TTtensan/NERD-HPC/software/src/basic.cpp

/*
 TOYOSHIKI Tiny BASIC for Arduino
 (C)2012 Tetsuya Suzuki
 GNU General Public License
 */

#include <stdlib.h>
#include <stdio.h>
#include "tusb.h"
#include "lcd.h"
#include "f_util.h"
#include "ff.h"
#include "font.h"
#include "diskio.h"
#include "sd.hpp"
#include "io.h"
#include "ir.h"
#include "ioexp.h"
#include "speaker.h"
#include "usb.h"
#include "basic.hpp"
#include "pin.h"

#define _FONT_
#define _SLEEP_
#define _PROG_
#define _LCD_
#define _USB_
#define _IO_
#define _IR_
#define _IOEXP_
#define _SPEAKER_

// TOYOSHIKI TinyBASIC symbols
// TO-DO Rewrite defined values to fit your machine as needed
#define SIZE_LINE 128 //Command line buffer length + NULL
#define SIZE_IBUF 128 //i-code conversion buffer size
#define SIZE_LIST 32768 //List buffer size
#define SIZE_ARRY 256 //Array area size
#define SIZE_GSTK 20 //GOSUB stack size(2/nest)
#define SIZE_LSTK 50 //FOR stack size(5/nest)

// Depending on device functions
// TO-DO Rewrite these functions to fit your machine
#define STR_EDITION "NERD HPC"
#define STR_VERSION "1.13.7"

// Terminal control
#define c_putch(c) putch2(c)
#define c_getch( ) getch2()
#define c_kbhit( ) kbhit2()

// シリアル出力のバッファ。
// 1文字ごとにprintf()を呼ぶと毎回stdioのロック取得とUSB CDCへの
// ブロッキング書き込みが走り、PRINTの実行時間の大半をここで使ってしまう。
// 改行かバッファが埋まるまで溜めて、まとめて書き出す
#define SIZE_OBUF 64
static char obuf[SIZE_OBUF];
static unsigned char obufi = 0;

void oflush() {
    if(obufi == 0) return;
    fwrite(obuf, 1, obufi, stdout);
    obufi = 0;
    fflush(stdout);
}

void putch2(char c) {
    obuf[obufi++] = c;
    if(obufi >= SIZE_OBUF || c == '\n') oflush();
    lcd_print_c_auto(c, black);
}

char getch2() {
    oflush(); // 入力待ちに入る前に溜まっている分を吐き出す
    while(true) {
        if(ioexp_getchr_available()) return ioexp_getchr();
        else if(tud_cdc_available()) return getchar();
    }
}

uint32_t kbhit2() {
    if(ioexp_getchr_available() || tud_cdc_available()) return 1;
    else return 0;
}

#define KEY_ENTER 13
void newline(void) {
  c_putch(13); //CR
  c_putch(10); //LF
}

// Return random number
short getrnd(short value) {
  return rand()%value + 1;
}

// Prototypes (necessity minimum)
short iexp(void);
void iload();

// Keyword table
const char *kwtbl[] = {
  "GOTO", "GOSUB", "RETURN",
  "FOR", "TO", "STEP", "NEXT",
  "IF", "REM", "STOP",
  "INPUT", "PRINT", "LET",
  ",", ";",
  "-", "+", "*", "/", "%", "(", ")",
  "$", "`", "<<", ">>",
  "&", "|", "^", "~",
  ">=", "#", ">", "=", "<=", "<",
  "@", "RND", "ABS", "SIZE",
#ifdef _FONT_
  "SETF",
  "RESETF",
#endif
#ifdef _SLEEP_
  "SLEEPMS",
  "SLEEPUS",
#endif
#ifdef _PROG_
  "SAVE", "LOAD", "DELETE",
#endif
#ifdef _LCD_
  "CLS",
  "GCLS",
  "VSYNC",
  "GPSET",
  "GLINE",
  "GRECT",
  "GCIRCLE",
  "GPLAYNM",
  "GPUTC",
  "CHR",
  "LOCATE",
  "SCR",
  "GPGET",
  "GTRI",
#endif
#ifdef _USB_
  "SNDKCD",
#endif
#ifdef _IO_
  "IOSD",
  "IOPUT",
  "IOGET",
  "IOPU",
  "IOPD",
  "IODP",
  "IOUS",
  "IOUR",
  "IOIIM",
  "IOIIS",
  "IOIS",
  "IOIR",
#endif
#ifdef _IR_
  "IRPUT",
  "IRGET",
#endif
#ifdef _IOEXP_
  "GKOPT",
  "GETKEY",
#endif
#ifdef _SPEAKER_
  "PLYSND",
  "STPSND",
#endif
  "LIST", "ALL", "RUN", "NEW"
};

// Keyword count
#define SIZE_KWTBL (sizeof(kwtbl) / sizeof(const char*))

// i-code(Intermediate code) assignment
enum {
  I_GOTO, I_GOSUB, I_RETURN,
  I_FOR, I_TO, I_STEP, I_NEXT,
  I_IF, I_REM, I_STOP,
  I_INPUT, I_PRINT, I_LET,
  I_COMMA, I_SEMI,
  I_MINUS, I_PLUS, I_MUL, I_DIV, I_MOD, I_OPEN, I_CLOSE,
  I_HEX, I_BIN, I_LSHIFT, I_RSHIFT,
  I_AND, I_OR, I_XOR, I_BITFLIP,
  I_GTE, I_SHARP, I_GT, I_EQ, I_LTE, I_LT,
  I_ARRAY, I_RND, I_ABS, I_SIZE,
#ifdef _FONT_
  I_SETF,
  I_RESETF,
#endif
#ifdef _SLEEP_
  I_SLEEPMS,
  I_SLEEPUS,
#endif
#ifdef _PROG_
  I_SAVE, I_LOAD, I_DELETE,
#endif
#ifdef _LCD_
  I_CLS,
  I_GCLS,
  I_VSYNC,
  I_GPSET,
  I_GLINE,
  I_GRECT,
  I_GCIRCLE,
  I_GPLAYNM,
  I_GPUTC,
  I_CHR,
  I_LOCATE,
  I_SCR,
  I_GPGET,
  I_GTRI,
#endif
#ifdef _USB_
  I_SNDKCD,
#endif
#ifdef _IO_
  I_IOSD,
  I_IOPUT,
  I_IOGET,
  I_IOPU,
  I_IOPD,
  I_IODP,
  I_IOUS,
  I_IOUR,
  I_IOIIM,
  I_IOIIS,
  I_IOIS,
  I_IOIR,
#endif
#ifdef _IR_
  I_IRPUT,
  I_IRGET,
#endif
#ifdef _IOEXP_
  I_GKOPT,
  I_GETKEY,
#endif
#ifdef _SPEAKER_
  I_PLYSND,
  I_STPSND,
#endif
  I_LIST, I_ALL, I_RUN, I_NEW,
  I_NUM, I_HEXNUM, I_BINNUM, I_VAR, I_STR,
  I_EOL
};

// List formatting condition
// 後ろに空白を入れない中間コード
const unsigned char i_nsa[] = {
  I_RETURN, I_STOP, I_COMMA,
  I_MINUS, I_PLUS, I_MUL, I_DIV, I_MOD, I_OPEN, I_CLOSE,
  I_HEX, I_BIN, I_LSHIFT, I_RSHIFT,
  I_AND, I_OR, I_XOR, I_BITFLIP,
  I_GTE, I_SHARP, I_GT, I_EQ, I_LTE, I_LT,
#ifdef _FONT_
  I_RESETF,
#endif
#ifdef _LCD_
  I_CLS,
  I_GCLS,
  I_VSYNC,
  I_SCR,
  I_GPGET,
#endif
#ifdef _IO_
  I_IOGET,
  I_IOUR,
  I_IOIIM,
  I_IOIIS,
  I_IOIR,
#endif
#ifdef _IR_
  I_IRGET,
#endif
#ifdef _IOEXP_
  I_GETKEY,
#endif
#ifdef _SPEAKER_
  I_STPSND,
#endif
  I_ARRAY, I_RND, I_ABS, I_SIZE, I_ALL
};

// 前が定数か変数のとき前の空白をなくす中間コード
const unsigned char i_nsb[] = {
  I_MINUS, I_PLUS, I_MUL, I_DIV, I_MOD, I_OPEN, I_CLOSE,
  I_HEX, I_BIN, I_LSHIFT, I_RSHIFT,
  I_AND, I_OR, I_XOR, I_BITFLIP,
  I_GTE, I_SHARP, I_GT, I_EQ, I_LTE, I_LT,
  I_COMMA, I_SEMI, I_EOL
};

// exception search function
char sstyle(unsigned char code,
  const unsigned char *table, unsigned char count) {
  while(count--) //中間コードの数だけ繰り返す
    if (code == table[count]) //もし該当の中間コードがあったら
      return 1; //1を持ち帰る
  return 0; //（なければ）0を持ち帰る
}

// exception search macro
#define nospacea(c) sstyle(c, i_nsa, sizeof(i_nsa))
#define nospaceb(c) sstyle(c, i_nsb, sizeof(i_nsb))

// Error messages
unsigned char err;// Error message index
const char* errmsg[] = {
  "OK",
  "Devision by zero",
  "Overflow",
  "Subscript out of range",
  "Icode buffer full",
  "List full",
  "GOSUB too many nested",
  "RETURN stack underflow",
  "FOR too many nested",
  "NEXT without FOR",
  "NEXT without counter",
  "NEXT mismatch FOR",
  "FOR without variable",
  "FOR without TO",
  "LET without variable",
  "IF without condition",
  "Undefined line number",
  "\'(\' or \')\' expected",
  "\'=\' expected",
  "Illegal command",
  "Syntax error",
  "Internal error",
#ifdef _PROG_
  "SD card mount error",
  "Change drive error",
  "File already exist",
  "File can not open",
  "File not found",
#endif
#ifdef _LCD_
  "SD card mount error",
  "Change drive error",
  "File not found",
#endif
  "Abort by [ESC]"
};

// Error code assignment
enum {
  ERR_OK,
  ERR_DIVBY0,
  ERR_VOF,
  ERR_SOR,
  ERR_IBUFOF, ERR_LBUFOF,
  ERR_GSTKOF, ERR_GSTKUF,
  ERR_LSTKOF, ERR_LSTKUF,
  ERR_NEXTWOV, ERR_NEXTUM, ERR_FORWOV, ERR_FORWOTO,
  ERR_LETWOV, ERR_IFWOC,
  ERR_ULN,
  ERR_PAREN, ERR_VWOEQ,
  ERR_COM,
  ERR_SYNTAX,
  ERR_SYS,
#ifdef _PROG_
  ERR_SDMOUNT,
  ERR_SDCHDRV,
  ERR_FEXIST,
  ERR_FNOPEN,
  ERR_FNFOUND,
#endif
#ifdef _LCD_
  ERR_NMSDMOUNT,
  ERR_NMSDCHDRV,
  ERR_NMFNFOUND,
#endif
  ERR_ESC
};

// RAM mapping
char lbuf[SIZE_LINE]; //Command line buffer
unsigned char ibuf[SIZE_IBUF]; //i-code conversion buffer
short var[26]; //Variable area
short arr[SIZE_ARRY]; //Array area
unsigned char listbuf[SIZE_LIST]; //List area
unsigned char* clp; //Pointer current line
unsigned char* cip; //Pointer current Intermediate code
unsigned char* gstk[SIZE_GSTK]; //GOSUB stack
unsigned char gstki; //GOSUB stack index
unsigned char* lstk[SIZE_LSTK]; //FOR stack
unsigned char lstki; //FOR stack index

// Standard C libraly (about) same functions
char c_toupper(char c) {
  return(c <= 'z' && c >= 'a' ? c - 32 : c);
}
char c_isprint(char c) {
  return(c >= 32 && c <= 126);
}
char c_isspace(char c) {
  return(c == ' ' || (c <= 13 && c >= 9));
}
char c_isdigit(char c) {
  return(c <= '9' && c >= '0');
}
char c_isalpha(char c) {
  return ((c <= 'z' && c >= 'a') || (c <= 'Z' && c >= 'A'));
}

void c_puts(const char *s) {
  while (*s) c_putch(*s++); //終端でなければ出力して繰り返す
}

void c_gets() {
  char c; //文字
  unsigned char len; //文字数

  len = 0; //文字数をクリア
  while ((c = c_getch()) != KEY_ENTER) { //改行でなければ繰り返す
    if (c == 9) c = ' '; //［Tab］キーは空白に置き換える
    //［BackSpace］キーが押された場合の処理（行頭ではないこと）
    if (((c == 8) || (c == 127)) && (len > 0)) {
      len--; //文字数を1減らす
      c_putch(8); c_putch(' '); c_putch(8); //文字を消す
    } else
    //表示可能な文字が入力された場合の処理（バッファのサイズを超えないこと）
    if (c_isprint(c) && (len < (SIZE_LINE - 1))) {
      lbuf[len++] = c; //バッファへ入れて文字数を1増やす
      c_putch(c); //表示
    }
  }
  newline(); //改行
  lbuf[len] = 0; //終端を置く

  if (len > 0) { //もしバッファが空でなければ
    while (c_isspace(lbuf[--len])); //末尾の空白を戻る
    lbuf[++len] = 0; //終端を置く
  }
}

// Print numeric specified columns
void putnum(short value, short d) {
  unsigned char dig; //桁位置
  unsigned char sign; //負号の有無（値を絶対値に変換した印）

  if (value < 0) { //もし値が0未満なら
    sign = 1; //負号あり
    value = -value; //値を絶対値に変換
  } else {
    sign = 0; //負号なし
  }

  lbuf[6] = 0; //終端を置く
  dig = 6; //桁位置の初期値を末尾に設定
  do { //次の処理をやってみる
    lbuf[--dig] = (value % 10) + '0'; //1の位を文字に変換して保存
    value /= 10; //1桁落とす
  } while (value > 0); //値が0でなければ繰り返す

  if (sign) //もし負号ありなら
    lbuf[--dig] = '-'; //負号を保存

  while (6 - dig < d) { //指定の桁数を下回っていれば繰り返す
    c_putch(' '); //桁の不足を空白で埋める
    d--; //指定の桁数を1減らす
  }
  c_puts(&lbuf[dig]); //桁位置からバッファの文字列を表示
}

// Input numeric and return value
// Called by only INPUT statement
short getnum() {
  short value, tmp; //値と計算過程の値
  char c; //文字
  unsigned char len; //文字数
  unsigned char sign; //負号

  len = 0; //文字数をクリア
  while ((c = c_getch()) != KEY_ENTER) { //改行でなければ繰り返す
    //［BackSpace］キーが押された場合の処理（行頭ではないこと）
    if (((c == 8) || (c == 127)) && (len > 0)) {
      len--; //文字数を1減らす
      c_putch(8); c_putch(' '); c_putch(8); //文字を消す
    } else
    //行頭の符号および数字が入力された場合の処理（符号込みで6桁を超えないこと）
    if ((len == 0 && (c == '+' || c == '-')) ||
      (len < 6 && c_isdigit(c))) {
      lbuf[len++] = c; //バッファへ入れて文字数を1増やす
      c_putch(c); //表示
    }
  }
  newline(); //改行
  lbuf[len] = 0; //終端を置く

  switch (lbuf[0]) { //先頭の文字で分岐
  case '-': //「-」の場合
    sign = 1; //負の値
    len = 1;  //数字列はlbuf[1]以降
    break;
  case '+': //「+」の場合
    sign = 0; //正の値
    len = 1;  //数字列はlbuf[1]以降
    break;
  default:  //どれにも該当しない場合
    sign = 0; //正の値
    len = 0;  //数字列はlbuf[0]以降
    break;
  }

  value = 0; //値をクリア
  tmp = 0; //計算過程の値をクリア
  while (lbuf[len]) { //終端でなければ繰り返す
    tmp = 10 * value + lbuf[len++] - '0'; //数字を値に変換
    if (value > tmp) { //もし計算過程の値が前回より小さければ
      err = ERR_VOF; //オーバーフローを記録
    }
    value = tmp; //計算過程の値を記録
  }

  if (sign) //もし負の値なら
    return -value; //負の値に変換して持ち帰る

  return value; //値を持ち帰る
}

bool is_hexchar(char c) {
  return (c >= '0' && c <= '9') ||
    (c >= 'A' && c <= 'F') ||
    (c >= 'a' && c <= 'f');
}

// 16進数の1文字を10進数の数値に変換
uint16_t hex2value(char hex) {
    if (hex >= '0' && hex <= '9') {
        return hex - '0'; // '0'〜'9' -> 0〜9
    } else if (hex >= 'A' && hex <= 'F') {
        return hex - 'A' + 10; // 'A'〜'F' -> 10〜15
    } else if (hex >= 'a' && hex <= 'f') {
        return hex - 'a' + 10; // 'a'〜'f' -> 10〜15
    } else {
        return -1; // 無効な文字
    }
}

// Convert token to i-code
// Return byte length or 0
unsigned char toktoi() {
  unsigned char i; //ループカウンタ（一部の処理で中間コードに相当）
  unsigned char len = 0; //中間コードの並びの長さ
  char* pkw = 0; //ひとつのキーワードの内部を指すポインタ
  char* ptok; //ひとつの単語の内部を指すポインタ
  char* s = lbuf; //文字列バッファの内部を指すポインタ
  char c; //文字列の括りに使われている文字（「"」または「'」）
  short value; //定数
  short tmp; //変換過程の定数

  uint16_t hex;
  uint16_t hcnt;
  uint16_t bin;
  uint16_t bcnt;

  while (*s) { //文字列1行分の終端まで繰り返す
    while (c_isspace(*s)) s++; //空白を読み飛ばす

    //キーワードテーブルで変換を試みる
    for (i = 0; i < SIZE_KWTBL; i++) { //全部のキーワードを試す
      pkw = (char *)kwtbl[i]; //キーワードの先頭を指す
      ptok = s; //単語の先頭を指す

      //キーワードと単語の比較
      while ( //次の条件が成立する限り繰り返す
      (*pkw != 0) && //キーワードの末尾に達していなくて
      (*pkw == c_toupper(*ptok))) { //文字が一致している
        pkw++; //キーワードの次の文字へ進む
        ptok++; //単語の次の文字へ進む
      }

      //キーワードと単語が一致した場合の処理
      if (*pkw == 0) { //もしキーワードの末尾に達していたら（変換成功）
        if (len >= SIZE_IBUF - 1) { //もし中間コードが長すぎたら
          err = ERR_IBUFOF; //エラー番号をセット
          return 0; //0を持ち帰る
        }

        ibuf[len++] = i; //中間コードを記録
        s = ptok; //文字列の処理ずみの部分を詰める
        break; //単語→中間コード1個分の変換を完了
      } //キーワードと単語が一致した場合の処理の末尾

    } //キーワードテーブルで変換を試みるの末尾

    // 参考[https://github.com/Tamakichi/ttbasic_arduino_stm32/blob/master/ttbasic/basic.cpp]
    // 16進数の変換を試みる
    if (i == I_HEX) {
      if (is_hexchar(*s)) {
        hex = 0;
        hcnt = 0;
        do {
          hex = (hex<<4) + hex2value(*s++);
          hcnt++;
        } while (is_hexchar(*s));
        if (hcnt > 4) {
          err = ERR_VOF;
          return 0;
        }
        if (len >= SIZE_IBUF - 3) {
          err = ERR_IBUFOF;
          return 0;
        }
        len--; // $を置き換えるために格納位置を移動
        ibuf[len++] = I_HEXNUM;
        ibuf[len++] = hex & 255;
        ibuf[len++] = hex >> 8;
      }
    }

    // 2進数の変換を試みる
    if (i == I_BIN) {
      if ( *s == '0'|| *s == '1' ) {
        bin = 0;
        bcnt = 0;
        do {
          bin = (bin<<1) + (*s++)-'0';
          bcnt++;
        } while (*s == '0'|| *s == '1');
        if (bcnt > 16) {
          err = ERR_VOF;
          return 0;
        }
        if (len >= SIZE_IBUF - 3) {
          err = ERR_IBUFOF;
          return 0;
        }
        len--;    // `を置き換えるために格納位置を移動
        ibuf[len++] = I_BINNUM;
        ibuf[len++] = bin & 255;
        ibuf[len++] = bin >> 8;
      }      
    }

    //コメントへの変換を試みる
    if(i == I_REM) { //もし中間コードがI_REMなら
      while (c_isspace(*s)) s++; //空白を読み飛ばす
      ptok = s; //コメントの先頭を指す

      for (i = 0; *ptok++; i++); //コメントの文字数を得る
      if (len >= SIZE_IBUF - 2 - i) { //もし中間コードが長すぎたら
        err = ERR_IBUFOF; //エラー番号をセット
        return 0; //0を持ち帰る
      }

      ibuf[len++] = i; //コメントの文字数を記録
      while (i--) { //コメントの文字数だけ繰り返す
        ibuf[len++] = *s++; //コメントを記録
      }
      break; //文字列の処理を打ち切る（終端の処理へ進む）
    }

    if (*pkw == 0) //もしすでにキーワードで変換に成功していたら
      continue; //繰り返しの先頭へ戻って次の単語を変換する

    ptok = s; //単語の先頭を指す

    //定数への変換を試みる
    if (c_isdigit(*ptok)) { //もし文字が数字なら
      value = 0; //定数をクリア
      tmp = 0; //変換過程の定数をクリア
      do { //次の処理をやってみる
        tmp = 10 * value + *ptok++ - '0'; //数字を値に変換
        if (value > tmp) { //もし前回の値より小さければ
          err = ERR_VOF; //エラー番号をセット
          return 0; //0を持ち帰る
        }
        value = tmp; //0を持ち帰る
      } while (c_isdigit(*ptok)); //文字が数字である限り繰り返す

      if (len >= SIZE_IBUF - 3) { //もし中間コードが長すぎたら
        err = ERR_IBUFOF; //エラー番号をセット
        return 0; //0を持ち帰る
      }
      ibuf[len++] = I_NUM; //中間コードを記録
      ibuf[len++] = value & 255; //定数の下位バイトを記録
      ibuf[len++] = value >> 8; //定数の上位バイトを記録
      s = ptok; //文字列の処理ずみの部分を詰める
    }
    else

    //文字列への変換を試みる
    if (*s == '\"' || *s == '\'') { //もし文字が「"」か「'」なら
      c = *s++; //「"」か「'」を記憶して次の文字へ進む
      ptok = s; //文字列の先頭を指す
      //文字列の文字数を得る
      for (i = 0; (*ptok != c) && c_isprint(*ptok); i++)
        ptok++;
      if (len >= SIZE_IBUF - 1 - i) { //もし中間コードが長すぎたら
        err = ERR_IBUFOF; //エラー番号をセット
        return 0; //0を持ち帰る
      }
      ibuf[len++] = I_STR; //中間コードを記録
      ibuf[len++] = i; //文字列の文字数を記録
      while (i--) { //文字列の文字数だけ繰り返す
        ibuf[len++] = *s++; //文字列を記録
      }
      if (*s == c) s++; //もし文字が「"」か「'」なら次の文字へ進む
    }
    else

    //変数への変換を試みる
    if (c_isalpha(*ptok)) { //もし文字がアルファベットなら
      if (len >= SIZE_IBUF - 2) { //もし中間コードが長すぎたら
        err = ERR_IBUFOF; //エラー番号をセット
        return 0; //0を持ち帰る
      }
      //もし変数が3個並んだら
      if (len >= 4 && ibuf[len - 2] == I_VAR && ibuf[len - 4] == I_VAR) {
        err = ERR_SYNTAX; //エラー番号をセット
        return 0; //0を持ち帰る
      }

      ibuf[len++] = I_VAR; //中間コードを記録
      ibuf[len++] = c_toupper(*ptok) - 'A'; //変数番号を記録
      s++; //次の文字へ進む
    }
    else

    //どれにも当てはまらなかった場合
    {
      err = ERR_SYNTAX; //エラー番号をセット
      return 0; //0を持ち帰る
    }
  } //文字列1行分の終端まで繰り返すの末尾

  ibuf[len++] = I_EOL; //文字列1行分の終端を記録
  return len; //中間コードの長さを持ち帰る
}

// Return free memory size
short getsize() {
  unsigned char* lp; //ポインタ

  for (lp = listbuf; *lp; lp += *lp); //ポインタを末尾へ移動
  return listbuf + SIZE_LIST - lp - 1; //残りを計算して持ち帰る
}

// Get line numbere by line pointer
short getlineno(unsigned char *lp) {
  if(*lp == 0) //もし末尾だったら
    return 32767; //行番号の最大値を持ち帰る
  return *(lp + 1) | *(lp + 2) << 8; //行番号を持ち帰る
}

// 行番号から行ポインタを引くキャッシュ。
// getlp()はリストの先頭からの線形探索なので、GOTO/GOSUBのたびに
// プログラム全体を舐めることになり、行数の多いプログラムでは
// ループ1周のコストが行数に比例して増えていく。
// 行番号を鍵にした直接マップで、分岐先の再探索を省く。
// リストを書き換えたらポインタが無効になるのでlpc_clear()すること
#define SIZE_LPCACHE 32 //2のべき乗であること
static short lpc_lineno[SIZE_LPCACHE]; //0は空きの印（行番号は1以上）
static unsigned char* lpc_lp[SIZE_LPCACHE];

void lpc_clear() {
  for (unsigned char i = 0; i < SIZE_LPCACHE; i++)
    lpc_lineno[i] = 0;
}

// Search line by line number
unsigned char* getlp(short lineno) {
  unsigned char *lp; //ポインタ
  unsigned char slot; //キャッシュの位置

  slot = (unsigned char)lineno & (SIZE_LPCACHE - 1);
  if (lpc_lineno[slot] == lineno) //もしキャッシュに入っていたら
    return lpc_lp[slot]; //探索せずに持ち帰る

  for (lp = listbuf; *lp; lp += *lp) //先頭から末尾まで繰り返す
    if (getlineno(lp) >= lineno) //もし指定の行番号以上なら
      break; //繰り返しを打ち切る

  //見つかった行だけを憶える。
  //指定より後ろの行やリスト末尾を憶えると、間の行が挿入されたときに
  //古い答えを返してしまう（挿入時にlpc_clear()するので実際には
  //起こらないが、憶える条件は狭くしておく）
  if (lineno > 0 && *lp && getlineno(lp) == lineno) {
    lpc_lineno[slot] = lineno;
    lpc_lp[slot] = lp;
  }

  return lp; //ポインタを持ち帰る
}

// Insert i-code to the list
void inslist() {
  unsigned char *insp; //挿入位置
  unsigned char *p1, *p2; //移動先と移動元
  short len; //移動の長さ

  if (getsize() < *ibuf) { //もし空きが不足していたら
    err = ERR_LBUFOF; //エラー番号をセット
    return; //処理を打ち切る
  }

  insp = getlp(getlineno(ibuf)); //挿入位置を取得

  lpc_clear(); //以降で行が動くのでキャッシュを捨てる

  //同じ行番号の行が存在したらとりあえず削除
  if (getlineno(insp) == getlineno(ibuf)) { //もし行番号が一致したら
    p1 = insp; //p1を挿入位置に設定
    p2 = p1 + *p1; //p2を次の行に設定
    while (len = *p2) { //次の行が末尾でなければ繰り返す
      while (len--) //次の行の長さだけ繰り返す
        *p1++ = *p2++; //前へ詰める
    }
    *p1 = 0; //リストの末尾に0を置く
  }

  //行番号だけが入力された場合はここで終わる
  if (*ibuf == 4) //もし長さが4（行番号のみ）なら
    return; //終了する

  //挿入のためのスペースを空ける
  for (p1 = insp; *p1; p1 += *p1); //p1をリストの末尾へ移動
  len = p1 - insp + 1; //移動する幅を計算
  p2 = p1 + *ibuf; //p2を末尾より1行の長さだけ後ろに設定
  while (len--) //移動する幅だけ繰り返す
    *p2-- = *p1--; //後ろへズラす

  //行を転送する
  len = *ibuf; //中間コードの長さを設定
  p1 = insp; //転送先を設定
  p2 = ibuf; //転送元を設定
  while (len--) //中間コードの長さだけ繰り返す
    *p1++ = *p2++; //転送
}

// 16進数の出力
void putHexnum(short value, uint8_t d) {

  uint16_t hex = (uint16_t)value;
  uint16_t h;
  uint16_t dig;

  if (hex >= 0x1000) dig = 4;
  else if (hex >= 0x100) dig = 3;
  else if (hex >= 0x10) dig = 2;
  else dig = 1;

  if (d != 0 && d > dig) dig = d;

  for (uint8_t i = 0; i < 4; i++) {
    h = ( hex >> (12 - i * 4) ) & 0x0f;
    lbuf[i] = h <= 9 ? h + '0': h + 'A' - 10;
  }
  lbuf[4] = 0;
  c_puts(&lbuf[4-dig]);
}

// 2進数の出力
void putBinnum(int16_t value, uint8_t d) {
  uint16_t bin = (uint16_t)value;
  uint16_t dig = 0;

  for (uint8_t i=0; i < 16; i++) {
    if ( (0x8000>>i) & bin ) {
      dig = 15 - i;
      break;
    }
  }
  dig++;
  
  if (d > dig) dig = d;

  for (int8_t i=dig-1; i>=0; i--)
    c_putch((bin & (1<<i)) ? '1':'0');

}

//Listing 1 line of i-code
void putlist(unsigned char* ip) {
  unsigned char i; //ループカウンタ

  while (*ip != I_EOL) { //行末でなければ繰り返す

    //キーワードの処理
    if (*ip < SIZE_KWTBL) { //もしキーワードなら
      c_puts(kwtbl[*ip]); //キーワードテーブルの文字列を表示
      if (!nospacea(*ip)) //もし例外にあたらなければ
        c_putch(' '); //空白を表示

      if (*ip == I_REM) { //もし中間コードがI_REMなら
        ip++; //ポインタを文字数へ進める
        i = *ip++; //文字数を取得してポインタをコメントへ進める
        while (i--) //文字数だけ繰り返す
          c_putch(*ip++); //ポインタを進めながら文字を表示
        return; //終了する
      }

      ip++;//ポインタを次の中間コードへ進める
    }
    else

    //定数の処理
    if (*ip == I_NUM) { //もし定数なら
      ip++; //ポインタを値へ進める
      putnum(*ip | *(ip + 1) << 8, 0); //値を取得して表示
      ip += 2; //ポインタを次の中間コードへ進める
      if (!nospaceb(*ip)) //もし例外にあたらなければ
        c_putch(' '); //空白を表示
    }
    else

    //16進数定数の処理
    if (*ip == I_HEXNUM) { //もし16進定数なら
      ip++; //ポインタを値へ進める
      c_putch('$'); //空白を表示
      putHexnum(*ip | *(ip + 1) << 8, 2); //値を取得して表示
      ip += 2; //ポインタを次の中間コードへ進める
      if (!nospaceb(*ip)) //もし例外にあたらなければ
        c_putch(' '); //空白を表示
    }
    else

    //2進数定数の処理
    if (*ip == I_BINNUM) { //もし2進定数なら
      ip++; //ポインタを値へ進める
      c_putch('`'); //"`"を表示
      if (*(ip + 1)) putBinnum(*ip | *(ip + 1) << 8, 16); //値を取得して16桁で表示
      else putBinnum(*ip, 8);  //値を取得して8桁で表示
      ip += 2; //ポインタを次の中間コードへ進める
      if (!nospaceb(*ip)) //もし例外にあたらなければ
        c_putch(' '); //空白を表示
    }
    else 

    //変数の処理
    if (*ip == I_VAR) { //もし定数なら
      ip++; //ポインタを変数番号へ進める
      c_putch(*ip++ + 'A'); //変数名を取得して表示
      if (!nospaceb(*ip)) //もし例外にあたらなければ
        c_putch(' '); //空白を表示
    }
    else

    //文字列の処理
    if (*ip == I_STR) { //もし文字列なら
      char c; //文字列の括りに使われている文字（「"」または「'」）

      //文字列の括りに使われている文字を調べる
      c = '\"'; //文字列の括りを仮に「"」とする
      ip++; //ポインタを文字数へ進める
      for (i = *ip; i; i--) //文字数だけ繰り返す
        if (*(ip + i) == '\"') { //もし「"」があれば
          c = '\''; //文字列の括りは「'」
          break; //繰り返しを打ち切る
        }

      //文字列を表示する
      c_putch(c); //文字列の括りを表示
      i = *ip++; //文字数を取得してポインタを文字列へ進める
      while (i--) //文字数だけ繰り返す
        c_putch(*ip++); //ポインタを進めながら文字を表示
      c_putch(c); //文字列の括りを表示
      if (*ip == I_VAR) //もし次の中間コードが変数だったら
        c_putch(' '); //空白を表示
    }

    else { //どれにも当てはまらなかった場合
      err = ERR_SYS; //エラー番号をセット
      return; //終了する
    }
  }
}

#ifdef _LCD_
void check_paren_open() {
  if (*cip != I_OPEN)  err = ERR_PAREN;
  else cip++;
}

void check_paren_close() {
  if (*cip != I_CLOSE)  err = ERR_PAREN;
  else cip++;
}

// 複数の引数がある際のgetparam
short getarg() {

  short value; //値

  value = iexp(); //式を計算
  if (err) //もしエラーが生じたら
    return 0; //終了

  return value; //値を持ち帰る

}
#endif

// Get argument in parenthesis
short getparam() {
  short value; //値

  if (*cip != I_OPEN) { //もし「(」でなければ
    err = ERR_PAREN; //エラー番号をセット
    return 0; //終了
  }
  cip++; //中間コードポインタを次へ進める

  value = iexp(); //式を計算
  if (err) //もしエラーが生じたら
    return 0; //終了

  if (*cip != I_CLOSE) { //もし「)」でなければ
    err = ERR_PAREN; //エラー番号をセット
    return 0; //終了
  }
  cip++; //中間コードポインタを次へ進める

  return value; //値を持ち帰る
}

#ifdef _LCD_
short iscr() {

  short x_pos, y_pos;
  short value;

  check_paren_open();
  if (err) return -1;

  x_pos = getarg();
  if (err) return -1;

  if (*cip != I_COMMA) {
    err = ERR_SYNTAX;
    return -1;
  }
  cip++;

  y_pos = getarg();
  if (err) return -1;

  check_paren_close();
  if (err) return -1;

  value = lcd_scr(x_pos, y_pos);
  return value;

}

short igpget() {

  short x_pos, y_pos;
  short value;

  check_paren_open();
  if (err) return -1;

  x_pos = getarg();
  if (err) return -1;

  if (*cip != I_COMMA) {
    err = ERR_SYNTAX;
    return -1;
  }
  cip++;

  y_pos = getarg();
  if (err) return -1;

  check_paren_close();
  if (err) return -1;

  value = lcd_pget(x_pos, y_pos);
  return value;

}
#endif

#ifdef _IO_
short iioget(short gpio) {

    short status = io_get(gpio);
    return status;
}

short iiour() {
    short data = io_uart_receive();
    return data;
}

short iioir() {
    short data = io_i2c_receive();
    return data;
}
#endif

#ifdef _IR_
short iirget() {
    short status = ir_get();
    return status;
}
#endif

#ifdef _IOEXP_

short igetkey(short index) {

    short keycode = ioexp_getkey(index);
    return keycode;
}
#endif


// Get value
short ivalue() {
  short value; //値

  switch (*cip) { //中間コードで分岐

  //定数の取得
  case I_NUM: //定数の場合
  case I_HEXNUM: // 16進数定数
  case I_BINNUM: // 2進数定数
    cip++; //中間コードポインタを次へ進める
    value = *cip | *(cip + 1) << 8; //定数を取得
    cip += 2; //中間コードポインタを定数の次へ進める
    break; //ここで打ち切る

  //+付きの値の取得
  case I_PLUS: //「+」の場合
    cip++; //中間コードポインタを次へ進める
    value = ivalue(); //値を取得
    break; //ここで打ち切る

  //負の値の取得
  case I_MINUS: //「-」の場合
    cip++; //中間コードポインタを次へ進める
    value = 0 - ivalue(); //値を取得して負の値に変換
    break; //ここで打ち切る

  case I_BITFLIP: // 「~」の場合
    cip++; //中間コードポインタを次へ進める
    value = ~((uint16_t)ivalue()); //値を取得してビット反転
    break;

  //変数の値の取得
  case I_VAR: //変数の場合
    cip++; //中間コードポインタを次へ進める
    value = var[*cip++]; //変数番号から変数の値を取得して次を指し示す
    break; //ここで打ち切る

  //括弧の値の取得
  case I_OPEN: //「(」の場合
    value = getparam(); //括弧の値を取得
    break; //ここで打ち切る

  //配列の値の取得
  case I_ARRAY: //配列の場合
    cip++; //中間コードポインタを次へ進める
    value = getparam(); //括弧の値を取得
    if (err) //もしエラーが生じたら
      break; //ここで打ち切る
    if (value >= SIZE_ARRY) { //もし添え字の上限を超えたら
      err = ERR_SOR; //エラー番号をセット
      break; //ここで打ち切る
    }
    value = arr[value]; //配列の値を取得
    break; //ここで打ち切る

#ifdef _LCD_
  case I_SCR: //関数SCRの場合
    cip++;
    value = iscr();
      if (err) //もしエラーが生じたら
        break; //ここで打ち切る
    break;

  case I_GPGET: //関数GPGETの場合
    cip++;
    value = igpget();
      if (err) //もしエラーが生じたら
        break; //ここで打ち切る
    break;
#endif

#ifdef _IO_
  case I_IOGET: //関数IOGETの場合
    cip++;
    value = getparam();
    if (err) //もしエラーが生じたら
      break; //ここで打ち切る
    if(value < 1 || 4 < value) {
        err = ERR_SYNTAX;
        break;
    }
    value = iioget(value);
    break;

  case I_IOUR: //関数IOURの場合
    cip++;
    //もし後ろに「()」がなかったら
    if ((*cip != I_OPEN) || (*(cip + 1) != I_CLOSE)) {
      err = ERR_PAREN; //エラー番号をセット
      break; //ここで打ち切る
    }
    cip += 2; //中間コードポインタを「()」の次へ進める
    value = iiour();
    break;

  case I_IOIR: //関数IOIRの場合
    cip++;
    //もし後ろに「()」がなかったら
    if ((*cip != I_OPEN) || (*(cip + 1) != I_CLOSE)) {
      err = ERR_PAREN; //エラー番号をセット
      break; //ここで打ち切る
    }
    cip += 2; //中間コードポインタを「()」の次へ進める
    value = iioir();
    break;
#endif

#ifdef _IR_
  case I_IRGET: //関数IRGETの場合
    cip++;
    //もし後ろに「()」がなかったら
    if ((*cip != I_OPEN) || (*(cip + 1) != I_CLOSE)) {
      err = ERR_PAREN; //エラー番号をセット
      break; //ここで打ち切る
    }
    cip += 2; //中間コードポインタを「()」の次へ進める
    value = iirget();
    break;
#endif

#ifdef _IOEXP_
  case I_GETKEY: //関数GETKEYの場合
    cip++;
    value = getparam();
    if (err) //もしエラーが生じたら
      break; //ここで打ち切る
    if(value < 0 || 7 < value) {
        err = ERR_SYNTAX;
        break;
    }
    value = igetkey(value);
    break;
#endif

  //関数の値の取得
  case I_RND: //関数RNDの場合
    cip++; //中間コードポインタを次へ進める
    value = getparam(); //括弧の値を取得
    if (err) //もしエラーが生じたら
      break; //ここで打ち切る
    value = getrnd(value); //乱数を取得
    break; //ここで打ち切る

  case I_ABS: //関数ABSの場合
    cip++; //中間コードポインタを次へ進める
    value = getparam(); //括弧の値を取得
    if (err) //もしエラーが生じたら
      break; //ここで打ち切る
    if(value < 0) //もし0未満なら
      value *= -1; //正負を反転
    break; //ここで打ち切る

  case I_SIZE: //関数SIZEの場合
    cip++; //中間コードポインタを次へ進める
    //もし後ろに「()」がなかったら
    if ((*cip != I_OPEN) || (*(cip + 1) != I_CLOSE)) {
      err = ERR_PAREN; //エラー番号をセット
      break; //ここで打ち切る
    }
    cip += 2; //中間コードポインタを「()」の次へ進める
    value = getsize(); //プログラム保存領域の空きを取得
    break; //ここで打ち切る

  default: //以上のいずれにも該当しなかった場合
    err = ERR_SYNTAX; //エラー番号をセット
    break; //ここで打ち切る
  }
  return value; //取得した値を持ち帰る
}

// multiply or divide calculation
short imul() {
  short value, tmp; //値と演算値

  value = ivalue(); //値を取得
  if (err) //もしエラーが生じたら
    return -1; //終了

  while (1) //無限に繰り返す
  switch(*cip){ //中間コードで分岐

  case I_MUL: //掛け算の場合
    cip++; //中間コードポインタを次へ進める
    tmp = ivalue(); //演算値を取得
    value *= tmp; //掛け算を実行
    break; //ここで打ち切る

  case I_DIV: //割り算の場合
    cip++; //中間コードポインタを次へ進める
    tmp = ivalue(); //演算値を取得
    if (tmp == 0) { //もし演算値が0なら
      err = ERR_DIVBY0; //エラー番号をセット
      return -1; //終了
    }
    value /= tmp; //割り算を実行
    break; //ここで打ち切る

  case I_MOD: //剰余の場合
    cip++; //中間コードポインタを次へ進める
    tmp = ivalue(); //演算値を取得
    if (tmp == 0) { //もし演算値が0なら
      err = ERR_DIVBY0; //エラー番号をセット
      return -1; //終了
    }
    value %= tmp; //割り算を実行
    break; 

  case I_LSHIFT: // シフト演算 "<<" の場合
    cip++; //中間コードポインタを次へ進める
    tmp = ivalue(); //演算値を取得
    value =((uint16_t)value)<<tmp;
    break;

  case I_RSHIFT: // シフト演算 ">>" の場合
    cip++; //中間コードポインタを次へ進める
    tmp = ivalue(); //演算値を取得
    value =((uint16_t)value)>>tmp;
    break; 

  case I_AND:  // 論理積(ビット演算)
    cip++; //中間コードポインタを次へ進める
    tmp = ivalue(); //演算値を取得
    value =((uint16_t)value)&((uint16_t)tmp);
    break; //ここで打ち切る

  case I_OR:   //論理和(ビット演算)
    cip++; //中間コードポインタを次へ進める
    tmp = ivalue(); //演算値を取得
    value =((uint16_t)value)|((uint16_t)tmp);
    break; 

  case I_XOR: //排他的論理和(ビット演算)
    cip++; //中間コードポインタを次へ進める
    tmp = ivalue(); //演算値を取得
    value =((uint16_t)value)^((uint16_t)tmp);
    break; //ここで打ち切る

  default: //以上のいずれにも該当しなかった場合
    return value; //値を持ち帰る
  } //中間コードで分岐の末尾
}

// add or subtract calculation
short iplus() {
  short value, tmp; //値と演算値

  value = imul(); //値を取得
  if (err) //もしエラーが生じたら
    return -1; //終了

  while (1) //無限に繰り返す
  switch(*cip){ //中間コードで分岐

  case I_PLUS: //足し算の場合
    cip++; //中間コードポインタを次へ進める
    tmp = imul(); //演算値を取得
    value += tmp; //足し算を実行
    break; //ここで打ち切る

  case I_MINUS: //引き算の場合
    cip++; //中間コードポインタを次へ進める
    tmp = imul(); //演算値を取得
    value -= tmp; //引き算を実行
    break; //ここで打ち切る

  default: //以上のいずれにも該当しなかった場合
    return value; //値を持ち帰る
  } //中間コードで分岐の末尾
}

// The parser
short iexp() {
  short value, tmp; //値と演算値

  value = iplus(); //値を取得
  if (err) //もしエラーが生じたら
    return -1; //終了

  // conditional expression 
  while (1) //無限に繰り返す
  switch(*cip){ //中間コードで分岐

  case I_EQ: //「=」の場合
    cip++; //中間コードポインタを次へ進める
    tmp = iplus(); //演算値を取得
    value = (value == tmp); //真偽を判定
    break; //ここで打ち切る
  case I_SHARP: //「#」の場合
    cip++; //中間コードポインタを次へ進める
    tmp = iplus(); //演算値を取得
    value = (value != tmp); //真偽を判定
    break; //ここで打ち切る
  case I_LT: //「<」の場合
    cip++; //中間コードポインタを次へ進める
    tmp = iplus(); //演算値を取得
    value = (value < tmp); //真偽を判定
    break; //ここで打ち切る
  case I_LTE: //「<=」の場合
    cip++; //中間コードポインタを次へ進める
    tmp = iplus(); //演算値を取得
    value = (value <= tmp); //真偽を判定
    break; //ここで打ち切る
  case I_GT: //「>」の場合
    cip++; //中間コードポインタを次へ進める
    tmp = iplus(); //演算値を取得
    value = (value > tmp); //真偽を判定
    break; //ここで打ち切る
  case I_GTE: //「>=」の場合
    cip++; //中間コードポインタを次へ進める
    tmp = iplus(); //演算値を取得
    value = (value >= tmp); //真偽を判定
    break; //ここで打ち切る

  default: //以上のいずれにも該当しなかった場合
    return value; //値を持ち帰る
  } //中間コードで分岐の末尾
}

#ifdef _LCD_
void ichr() {

  short value;

  check_paren_open();
  if (err) return;

  while(true) {
    value = getarg();
    if (err) return;
    c_putch(value);
    if (*cip == I_COMMA) {
      cip++;
      continue;
    }
    break;
  }

  check_paren_close();
  if (err) return;
}
#endif

// 16進数文字出力
void ihex() {
  short value; // 値
  short d = 0; // 桁数(0で桁数指定なし)

  check_paren_open();
  if (err) return;
  value = getparam();
  if(err) return;
  if (*cip == I_COMMA) {
    cip++;
    d = getparam();
    if(err) return;
  }
  check_paren_close();
  if (err) return;
  putHexnum(value, d);    
}

// 2進数出力
void ibin() {
  int16_t value; // 値
  int16_t d = 0; // 桁数(0で桁数指定なし)

  check_paren_open();
  if (err) return;
  value = getparam();
  if(err) return;
  if (*cip == I_COMMA) {
    cip++;
    d = getparam();
    if(err) return;
  }
  check_paren_close();
  if (err) return;
  putBinnum(value, d);    
}

// PRINT handler
void iprint() {
  short value; //値
  short len; //桁数
  unsigned char i; //文字数

  len = 0; //桁数を初期化
  while (*cip != I_SEMI && *cip != I_EOL) { //文末まで繰り返す
    switch (*cip) { //中間コードで分岐

    case I_STR: //文字列の場合
      cip++; //中間コードポインタを次へ進める
      i = *cip++; //文字数を取得
      while (i--) //文字数だけ繰り返す
        c_putch(*cip++); //文字を表示
      break; //打ち切る

    case I_SHARP: //「#」の場合
      cip++; //中間コードポインタを次へ進める
      len = iexp(); //桁数を取得
      if (err) //もしエラーが生じたら
        return; //終了
      break; //打ち切る

    case I_HEX:
      cip++; //中間コードポインタを次へ進める
      ihex();
      if (err) //もしエラーが生じたら
        return; //終了
      break;
    case I_BIN:
      cip++; //中間コードポインタを次へ進める
      ibin();
      if (err) //もしエラーが生じたら
        return; //終了
      break;

#ifdef _LCD_
    case I_CHR: //CHR()の場合
      cip++; //中間コードポインタを次へ進める
      ichr();
      if (err) //もしエラーが生じたら
        return; //終了
      break;
#endif

    default: //以上のいずれにも該当しなかった場合（式とみなす）
      value = iexp(); //値を取得
      if (err) //もしエラーが生じたら
        return; //終了
      putnum(value, len); //値を表示
      break; //打ち切る
    } //中間コードで分岐の末尾

    if (*cip == I_COMMA) { //もしコンマがあったら
      cip++; //中間コードポインタを次へ進める
      if (*cip == I_SEMI || *cip == I_EOL) //もし文末なら
        return; //終了
    } else { //コンマがなければ
      if (*cip != I_SEMI && *cip != I_EOL) { //もし文末でなければ
        err = ERR_SYNTAX; //エラー番号をセット
        return; //終了
      }
    }
  } //文末まで繰り返すの末尾

  newline(); //改行
}

// INPUT handler
void iinput() {
  short value; //値
  short index; //配列の添え字
  unsigned char i; //文字数
  unsigned char prompt; //プロンプト表示フラグ

  while (1) { //無限に繰り返す
    prompt = 1; //まだプロンプトを表示していない

    //プロンプトが指定された場合の処理
    if(*cip == I_STR){ //もし中間コードが文字列なら
      cip++; //中間コードポインタを次へ進める
      i = *cip++; //文字数を取得
      while (i--) //文字数だけ繰り返す
        c_putch(*cip++); //文字を表示
      prompt = 0; //プロンプトを表示した
    }

    //値を入力する処理
    switch (*cip) { //中間コードで分岐
    case I_VAR: //変数の場合
      cip++; //中間コードポインタを次へ進める
      if (prompt) { //もしまだプロンプトを表示していなければ
        c_putch(*cip + 'A'); //変数名を表示
        c_putch(':'); //「:」を表示
      }
      value = getnum(); //値を入力
      if (err) //もしエラーが生じたら
        return; //終了
      var[*cip++] = value; //変数へ代入
      break; //打ち切る

    case I_ARRAY: //配列の場合
      cip++; //中間コードポインタを次へ進める
      index = getparam(); //配列の添え字を取得
      if (err) //もしエラーが生じたら
        return; //終了
      if (index >= SIZE_ARRY) { //もし添え字が上限を超えたら
        err = ERR_SOR; //エラー番号をセット
        return; //終了
      }
      if (prompt) { //もしまだプロンプトを表示していなければ
        c_puts("@("); //「@(」を表示
        putnum(index, 0); //添え字を表示
        c_puts("):"); //「):」を表示
      }
      value = getnum(); //値を入力
      if (err) //もしエラーが生じたら
        return; //終了
      arr[index] = value; //配列へ代入
      break; //打ち切る

    default: //以上のいずれにも該当しなかった場合
      err = ERR_SYNTAX; //エラー番号をセット
      return; //終了
    } //中間コードで分岐の末尾

    //値の入力を連続するかどうか判定する処理
    switch (*cip) { //中間コードで分岐
    case I_COMMA: //コンマの場合
      cip++; //中間コードポインタを次へ進める
      break; //打ち切る
    case I_SEMI: //「;」の場合
    case I_EOL: //行末の場合
      return; //終了
    default: //以上のいずれにも該当しなかった場合
      err = ERR_SYNTAX; //エラー番号をセット
      return; //終了
    } //中間コードで分岐の末尾
  } //無限に繰り返すの末尾
}

// Variable assignment handler
void ivar() {
  short value; //値
  short index; //変数番号

  index = *cip++; //変数番号を取得して次へ進む

  if (*cip != I_EQ) { //もし「=」でなければ
    err = ERR_VWOEQ; //エラー番号をセット
    return; //終了
  }
  cip++; //中間コードポインタを次へ進める

  //値の取得と代入
  value = iexp(); //式の値を取得
  if (err) //もしエラーが生じたら
    return; //終了
  var[index] = value; //変数へ代入
}

// Array assignment handler
void iarray() {
  short value; //値
  short index; //配列の添え字

  index = getparam(); //配列の添え字を取得
  if (err) //もしエラーが生じたら
    return; //終了

  if (index >= SIZE_ARRY) { //もし添え字が上限を超えたら
    err = ERR_SOR; //エラー番号をセット
    return; //終了
  }

  if (*cip != I_EQ) { //もし「=」でなければ
    err = ERR_VWOEQ; //エラー番号をセット
    return; //終了
  }
  cip++; //中間コードポインタを次へ進める

  value = iexp(); //式の値を取得
  if (err) //もしエラーが生じたら
    return; //終了
  arr[index] = value; //配列へ代入
}

// LET handler
void ilet() {
  switch (*cip) { //中間コードで分岐

  case I_VAR: //変数の場合
    cip++; //中間コードポインタを次へ進める
    ivar(); //変数への代入を実行
    break; //打ち切る

  case I_ARRAY: //配列の場合
    cip++; //中間コードポインタを次へ進める
    iarray(); //配列への代入を実行
    break; //打ち切る

  default: //以上のいずれにも該当しなかった場合
    err = ERR_LETWOV; //エラー番号をセット
    break; //打ち切る
  }
}

#ifdef _FONT_
void isetf() {

  short c_code;
  char buf[256];
  unsigned char len;
  unsigned char i;

  c_code = iexp();
  if(err) return;

  if (*cip != I_COMMA) {
    err = ERR_SYNTAX;
    return;
  }
  cip++;

  if (*cip != I_STR) {
    err = ERR_SYNTAX;
    return;
  }
  cip++;

  len = *cip;
  if (len == 0) {
    err = ERR_SYNTAX;
    return;
  }
  cip++;

  for (i = 0; i < len; i++) buf[i] = *cip++;
  buf[i] = 0;

  if (*cip != I_EOL && *cip != I_SEMI) { //もし文末でなければ
    err = ERR_SYNTAX;
    return;
  }

  font_setfont(c_code, buf);

}

void iresetf() {

  font_init();

}
#endif

#ifdef _SLEEP_
void isleepms() {

    short ms;
    ms = iexp();

    if(err) return;

    if(ms < 0) {
        err = ERR_SYNTAX;
        return;
    }

    // 単純にsleep_ms()で待つとその間キースキャンが完全に止まるので、
    // 1msずつ刻んでスキャンを回しながら待つ
    absolute_time_t end = make_timeout_time_ms(ms);
    while(absolute_time_diff_us(get_absolute_time(), end) > 0) {
        ioexp_task();
        sleep_ms(1);
    }
}

void isleepus() {

    short us;
    us = iexp();

    if(err) return;

    if(us < 0) {
        err = ERR_SYNTAX;
        return;
    }

    sleep_us(us);
}
#endif

#ifdef _LCD_
void icls() {

    lcd_cls(white, text);
}

void igcls() {

    lcd_cls(white, graphic);
}

void ivsync() {

    lcd_vsync();
}

void igpset() {

    short x_pos, y_pos, color; //値
    x_pos = iexp(); //値を取得
    if(err) return;
    cip++;
    y_pos = iexp();
    if(err) return;
    cip++;
    color = iexp();
    if(err) return;

    if(color) lcd_pset(x_pos, y_pos, black, graphic);
    else lcd_pset(x_pos, y_pos, white, graphic);
}

void igline() {

    short x_pos0, y_pos0, x_pos1, y_pos1, color;
    x_pos0 = iexp(); //値を取得
    if(err) return;
    cip++;
    y_pos0 = iexp();
    if(err) return;
    cip++;
    x_pos1 = iexp();
    if(err) return;
    cip++;
    y_pos1 = iexp();
    if(err) return;
    cip++;
    color = iexp();
    if(err) return;

    if(color) lcd_line(x_pos0, y_pos0, x_pos1, y_pos1, black);
    else lcd_line(x_pos0, y_pos0, x_pos1, y_pos1, white);
}

void igrect() {

    short x_pos0, y_pos0, x_pos1, y_pos1, color, fill;
    x_pos0 = iexp(); //値を取得
    if(err) return;
    cip++;
    y_pos0 = iexp();
    if(err) return;
    cip++;
    x_pos1 = iexp();
    if(err) return;
    cip++;
    y_pos1 = iexp();
    if(err) return;
    cip++;
    color = iexp();
    if(err) return;
    cip++;
    fill = iexp();
    if(err) return;

    if(color) lcd_rect(x_pos0, y_pos0, x_pos1, y_pos1, black, fill);
    else lcd_rect(x_pos0, y_pos0, x_pos1, y_pos1, white, fill);
}

void igcircle() {

    short x_pos, y_pos, radius, color, fill;
    x_pos = iexp(); //値を取得
    if(err) return;
    cip++;
    y_pos = iexp();
    if(err) return;
    cip++;
    radius = iexp();
    if(err) return;
    cip++;
    color = iexp();
    if(err) return;
    cip++;
    fill = iexp();
    if(err) return;

    if(color) lcd_circle(x_pos, y_pos, radius, black, fill);
    else lcd_circle(x_pos, y_pos, radius, white, fill);
}

void igplaynm() {

    FIL fp;
    char buf[256];
    unsigned char len;
    unsigned char i;

    if (*cip != I_STR) {
        err = ERR_SYNTAX;
        return;
    }
    cip++;

    len = *cip;
    if (len == 0) {
        err = ERR_SYNTAX;
        return;
    }
    cip++;

    for (i = 0; i < len; i++) buf[i] = *cip++;
    buf[i] = 0;

    if (*cip != I_EOL) {
        err = ERR_SYNTAX;
        return;
    }

    int result = lcd_play_nbm(0, 0, buf, black, false, 0, 13113);
    switch(result) {
        case LCD_ERR_SDMOUNT:
            err = ERR_NMSDMOUNT;
            return;
        case LCD_ERR_CHDRIVE:
            err = ERR_NMSDCHDRV;
            return;
        case LCD_ERR_FNFOUND:
            err = ERR_NMFNFOUND;
            return;
    }
}

void igputc() {

    short x_pos, y_pos, c_code, color, transparent;
    x_pos = iexp(); //値を取得
    if(err) return;
    cip++;
    y_pos = iexp();
    if(err) return;
    cip++;
    c_code = iexp();
    if(err) return;
    cip++;
    color = iexp();
    if(err) return;
    cip++;
    transparent = iexp();
    if(err) return;

    if(color) lcd_gprint_c_free(x_pos, y_pos, c_code, black, transparent);
    else lcd_gprint_c_free(x_pos, y_pos, c_code, white, transparent);

}

void ilocate() {

    short x_pos, y_pos;
    x_pos = iexp();
    if(err) return;
    cip++;
    y_pos = iexp();
    if(err) return;

    lcd_set_cursor(x_pos, y_pos);

}

void igtri() {

    short x_pos0, y_pos0, x_pos1, y_pos1, x_pos2, y_pos2, color, fill;
    x_pos0 = iexp(); //値を取得
    if(err) return;
    cip++;
    y_pos0 = iexp();
    if(err) return;
    cip++;
    x_pos1 = iexp();
    if(err) return;
    cip++;
    y_pos1 = iexp();
    if(err) return;
    cip++;
    x_pos2 = iexp();
    if(err) return;
    cip++;
    y_pos2 = iexp();
    if(err) return;
    cip++;
    color = iexp();
    if(err) return;
    cip++;
    fill = iexp();
    if(err) return;

    if(color) lcd_triangle(x_pos0, y_pos0, x_pos1, y_pos1, x_pos2, y_pos2, black, fill);
    else lcd_triangle(x_pos0, y_pos0, x_pos1, y_pos1, x_pos2, y_pos2, white, fill);
}
#endif

#ifdef _USB_
void isndkcd() {

    uint8_t keycode[6] = {};
    keycode[0] = (uint8_t)iexp();
    if(err) return;
    cip++;
    keycode[1] = (uint8_t)iexp();
    if(err) return;
    cip++;
    keycode[2] = (uint8_t)iexp();
    if(err) return;
    cip++;
    keycode[3] = (uint8_t)iexp();
    if(err) return;
    cip++;
    keycode[4] = (uint8_t)iexp();
    if(err) return;
    cip++;
    keycode[5] = (uint8_t)iexp();
    if(err) return;

    usb_set_keycode(keycode);
}
#endif

#ifdef _IO_
void iiosd() {

    short gpio,out;
    gpio = iexp(); //値を取得
    if(err) return;
    if(gpio < 1 || 4 < gpio) {
        err = ERR_SYNTAX;
        return;
    }
    cip++;
    out = iexp();
    if(err) return;

    io_set_dir(gpio, !out);
}

void iiopu() {

    short gpio;
    gpio = iexp(); //値を取得
    if(err) return;
    if(gpio < 1 || 4 < gpio) {
        err = ERR_SYNTAX;
        return;
    }

    io_pull_up(gpio);
}

void iiopd() {

    short gpio;
    gpio = iexp(); //値を取得
    if(err) return;
    if(gpio < 1 || 4 < gpio) {
        err = ERR_SYNTAX;
        return;
    }

    io_pull_down(gpio);
}

void iiodp() {

    short gpio;
    gpio = iexp(); //値を取得
    if(err) return;
    if(gpio < 1 || 4 < gpio) {
        err = ERR_SYNTAX;
        return;
    }

    io_disable_pulls(gpio);
}

void iioput() {

    short gpio, value;
    gpio = iexp(); //値を取得
    if(err) return;
    if(gpio < 1 || 4 < gpio) {
        err = ERR_SYNTAX;
        return;
    }
    cip++;
    value = iexp();
    if(err) return;

    io_put(gpio, value);
}

void iious() {

    short data;
    data = iexp(); //値を取得
    if(err) return;
    if(data < 0 || 255 < data) {
        err = ERR_SYNTAX;
        return;
    }

    io_uart_send((uint8_t)data);
}

void iioiim() {

    io_i2c_master_init();
}

void iioiis() {

    io_i2c_slave_init();
}

void iiois() {

    short data;
    data = iexp(); //値を取得
    if(err) return;
    if(data < 0 || 255 < data) {
        err = ERR_SYNTAX;
        return;
    }

    uint8_t send_data;
    send_data = (uint8_t)data;

    io_i2c_send(send_data);
}
#endif

#ifdef _IR_
void iirput() {

    short value;
    value = iexp();
    if(err) return;

    ir_put(value);

}
#endif

#ifdef _IOEXP_

void igkopt() {

    g_en_shift = iexp(); //値を取得
    if(err) return;
    cip++;
    g_en_esc = iexp();
    if(err) return;
}
#endif

#ifdef _SPEAKER_
void iplysnd() {

    short freq, duration_ms; //値
    freq = iexp(); //値を取得
    if(err) return;
    cip++;
    duration_ms = iexp();
    if(err) return;

    play_sound(freq, duration_ms);
}

void istpsnd() {

    stop_sound();
}
#endif

// 何文に1回［ESC］の確認をするか。2のべき乗であること
#define ESC_CHECK_INTERVAL 16
static unsigned short esc_check_count = 0;

// Execute a series of i-code
unsigned char* iexe() {
  short lineno; //行番号
  unsigned char* lp; //未確定の（エラーかもしれない）行ポインタ
  short index, vto, vstep; //FOR文の変数番号、終了値、増分
  short condition; //IF文の条件値

  while (*cip != I_EOL) { //行末まで繰り返す

  //強制的な中断の判定。
  //c_kbhit()はキースキャンとTinyUSBのコア跨ぎの問い合わせを伴うので、
  //1文ごとに通すとタイトなFORループでは無視できない。
  //キースキャン自体がIOEXP_SCAN_INTERVAL_MS(10ms)間隔で間引かれており、
  //ESCの応答性はそちらで律速されているため、ここを間引いても体感は変わらない
    if ((++esc_check_count & (ESC_CHECK_INTERVAL - 1)) == 0)
      if (c_kbhit()) //もし未読文字があったら
        if (c_getch() == 27) { //読み込んでもし［ESC］キーだったら
#ifdef _SPEAKER_
          stop_sound(); //鳴りっぱなしにならないよう、STPSNDと同じ処理で音を止める
#endif
          err = ERR_ESC; //エラー番号をセット
          break; //打ち切る
        }

    //中間コードを実行
    switch (*cip) { //中間コードで分岐

    case I_GOTO: //GOTOの場合
      cip++; //中間コードポインタを次へ進める
      lineno = iexp(); //分岐先の行番号を取得
      if (err) //もしエラーが生じたら
        break; //打ち切る
      lp = getlp(lineno); //分岐先のポインタを取得
      if (lineno != getlineno(lp)) { //もし分岐先が存在しなければ
        err = ERR_ULN; //エラー番号をセット
        break; //打ち切る
      }

      clp = lp; //行ポインタを分岐先へ更新
      cip = clp + 3; //中間コードポインタを先頭の中間コードに更新
      break; //打ち切る

    case I_GOSUB: //GOSUBの場合
      cip++; //中間コードポインタを次へ進める
      lineno = iexp(); //分岐先の行番号を取得
      if (err) //もしエラーが生じたら
        break; //打ち切る
      lp = getlp(lineno); //分岐先のポインタを取得
      if (lineno != getlineno(lp)) { //もし分岐先が存在しなければ
        err = ERR_ULN; //エラー番号をセット
        break; //打ち切る
      }

      //ポインタを退避
      if (gstki >= SIZE_GSTK - 2) { //もしGOSUBスタックがいっぱいなら
        err = ERR_GSTKOF; //エラー番号をセット
        break; //打ち切る
      }
      gstk[gstki++] = clp; //行ポインタを退避
      gstk[gstki++] = cip; //中間コードポインタを退避

      clp = lp; //行ポインタを分岐先へ更新
      cip = clp + 3; //中間コードポインタを先頭の中間コードに更新
      break; //打ち切る

    case I_RETURN: //RETURNの場合
      if (gstki < 2) { //もしGOSUBスタックが空なら
        err = ERR_GSTKUF; //エラー番号をセット
        break; //打ち切る
      }

      cip = gstk[--gstki]; //行ポインタを復帰
      clp = gstk[--gstki]; //中間コードポインタを復帰
      break; //打ち切る

    case I_FOR: //FORの場合
      cip++; //中間コードポインタを次へ進める

      //変数名を取得して開始値を代入（例I=1）
      if (*cip++ != I_VAR) { //もし変数がなかったら
        err = ERR_FORWOV; //エラー番号をセット
        break; //打ち切る
      }
      index = *cip; //変数名を取得
      ivar(); //代入文を実行
      if (err) //もしエラーが生じたら
        break; //打ち切る

      //終了値を取得（例TO 5）
      if (*cip == I_TO) { //もしTOだったら
        cip++; //中間コードポインタを次へ進める
        vto = iexp(); //終了値を取得
      } else { //TOではなかったら
        err = ERR_FORWOTO; //エラー番号をセット
        break; //打ち切る
      }

      //増分を取得（例STEP 1）
      if (*cip == I_STEP) { //もしSTEPだったら
        cip++; //中間コードポインタを次へ進める
        vstep = iexp(); //増分を取得
      } else //STEPではなかったら
        vstep = 1; //増分を1に設定

      //もし変数がオーバーフローする見込みなら
      if (((vstep < 0) && (-32767 - vstep > vto)) ||
        ((vstep > 0) && (32767 - vstep < vto))){
        err = ERR_VOF; //エラー番号をセット
        break; //打ち切る
      }

      //繰り返し条件を退避
      if (lstki >= SIZE_LSTK - 5) { //もしFORスタックがいっぱいなら
        err = ERR_LSTKOF; //エラー番号をセット
        break; //打ち切る
      }
      lstk[lstki++] = clp; //行ポインタを退避
      lstk[lstki++] = cip; //中間コードポインタを退避
      //FORスタックに終了値、増分、変数名を退避
      //Special thanks hardyboy
      lstk[lstki++] = (unsigned char*)(uintptr_t)vto;
      lstk[lstki++] = (unsigned char*)(uintptr_t)vstep;
      lstk[lstki++] = (unsigned char*)(uintptr_t)index;
      break; //打ち切る

    case I_NEXT: //NEXTの場合
      cip++; //中間コードポインタを次へ進める
      if (lstki < 5) { //もしFORスタックが空なら
        err = ERR_LSTKUF; //エラー番号をセット
        break; //打ち切る
      }

      //変数名を復帰
      index = (short)(uintptr_t)lstk[lstki - 1]; //変数名を復帰
      if (*cip++ != I_VAR) { //もしNEXTの後ろに変数がなかったら
        err = ERR_NEXTWOV; //エラー番号をセット
        break; //打ち切る
      }
      if (*cip++ != index) { //もし復帰した変数名と一致しなかったら
        err = ERR_NEXTUM; //エラー番号をセット
        break; //打ち切る
      }

      vstep = (short)(uintptr_t)lstk[lstki - 2]; //増分を復帰
      var[index] += vstep; //変数の値を最新の開始値に更新
      vto = (short)(uintptr_t)lstk[lstki - 3]; //終了値を復帰

      //もし変数の値が終了値を超えていたら
      if (((vstep < 0) && (var[index] < vto)) ||
        ((vstep > 0) && (var[index] > vto))) {
        lstki -= 5; //FORスタックを1ネスト分戻す
        break; //打ち切る
      }

      //開始値が終了値を超えていなかった場合
      cip = lstk[lstki - 4]; //行ポインタを復帰
      clp = lstk[lstki - 5]; //中間コードポインタを復帰
      break; //打ち切る

    case I_IF: //IFの場合
      cip++; //中間コードポインタを次へ進める
      condition = iexp(); //真偽を取得
      if (err) { //もしエラーが生じたら
        err = ERR_IFWOC; //エラー番号をセット
        break; //打ち切る
      }
      if (condition) //もし真なら
        break; //打ち切る（次の文を実行する）
      //偽の場合の処理はREMと同じ

    case I_REM: //REMの場合
      while (*cip != I_EOL) //I_EOLに達するまで繰り返す
        cip++; //中間コードポインタを次へ進める
      break; //打ち切る

    case I_STOP: //STOPの場合
      while (*clp) //リストの終端まで繰り返す
        clp += *clp; //行ポインタを次へ進める
      return clp; //行ポインタを持ち帰る

    //一般の文に相当する中間コードの照合と処理
    case I_VAR: //変数の場合（LETを省略した代入文）
      cip++; //中間コードポインタを次へ進める
      ivar(); //代入文を実行
      break; //打ち切る
    case I_ARRAY: //配列の場合（LETを省略した代入文）
      cip++; //中間コードポインタを次へ進める
      iarray(); //代入文を実行
      break; //打ち切る
    case I_LET: //LETの場合
      cip++; //中間コードポインタを次へ進める
      ilet(); //LET文を実行
      break; //打ち切る
    case I_PRINT: //PRINTの場合
      cip++; //中間コードポインタを次へ進める
      iprint(); //PRINT文を実行
      break; //打ち切る
    case I_INPUT: //INPUTの場合
      cip++; //中間コードポインタを次へ進める
      iinput(); //INPUT文を実行
      break; //打ち切る
#ifdef _FONT_
    case I_SETF:
        cip++;
        isetf();
        break;
    case I_RESETF:
        cip++;
        iresetf();
        break;
#endif
#ifdef _SLEEP_
    case I_SLEEPMS:
        cip++;
        isleepms();
        break;
    case I_SLEEPUS:
        cip++;
        isleepus();
        break;
#endif
#ifdef _PROG_
    case I_SAVE: //中間コードがSAVEの場合
    case I_LOAD: //中間コードがLOADの場合
    case I_DELETE: //中間コードがDELETEの場合
#endif
#ifdef _LCD_
    case I_CLS: //中間コードがCLSの場合
      cip++;
      icls();
      break;
    case I_GCLS: //中間コードがGCLSの場合
      cip++;
      igcls();
      break;
    case I_VSYNC: //中間コードがVSYNCの場合
      cip++;
      ivsync();
      break;
    case I_GPSET: //中間コードがGPSETの場合
      cip++;
      igpset();
      break;
    case I_GLINE: //中間コードがGLINEの場合
      cip++;
      igline();
      break;
    case I_GRECT: //中間コードがGRECTの場合
      cip++;
      igrect();
      break;
    case I_GCIRCLE: //中間コードがGCIRCLEの場合
      cip++;
      igcircle();
      break;
    case I_GPLAYNM: //中間コードがGPLAYNMの場合
      cip++;
      igplaynm();
      break;
    case I_GPUTC: //中間コードがGPUTCの場合
      cip++;
      igputc();
      break;
    case I_LOCATE: //中間コードがLOCATEの場合
      cip++;
      ilocate();
      break;
    case I_GTRI: //中間コードがGTRIの場合
      cip++;
      igtri();
      break;
#endif
#ifdef _USB_
    case I_SNDKCD: //中間コードがSNDKCDの場合
      cip++;
      isndkcd();
      break;
#endif
#ifdef _IO_
    case I_IOSD: //中間コードがIOSDの場合
      cip++;
      iiosd();
      break;
    case I_IOPUT: //中間コードがIOPUTの場合
      cip++;
      iioput();
      break;
    case I_IOPU: //中間コードがIOPUの場合
      cip++;
      iiopu();
      break;
    case I_IOPD: //中間コードがIOPDの場合
      cip++;
      iiopd();
      break;
    case I_IODP: //中間コードがIODPの場合
      cip++;
      iiodp();
      break;
    case I_IOUS: //中間コードがIOUSの場合
      cip++;
      iious();
      break;
    case I_IOIIM: //中間コードがIOIIMの場合
      cip++;
      iioiim();
      break;
    case I_IOIIS: //中間コードがIOIISの場合
      cip++;
      iioiis();
      break;
    case I_IOIS: //中間コードがIOISの場合
      cip++;
      iiois();
      break;
#endif
#ifdef _IR_
    case I_IRPUT: // 中間コードがIRPUTの場合
      cip++;
      iirput();
      break;
#endif
#ifdef _IOEXP_
    case I_GKOPT: //中間コードがGKOPTの場合
      cip++;
      igkopt();
      break;
#endif
#ifdef _SPEAKER_
    case I_PLYSND: //中間コードがPLYSNDの場合
      cip++;
      iplysnd();
      break;
    case I_STPSND: //中間コードがSTPSNDの場合
      cip++;
      istpsnd();
      break;
#endif
    case I_NEW: //中間コードがNEWの場合
    case I_LIST: //中間コードがLISTの場合
    case I_RUN: //中間コードがRUNの場合
      err = ERR_COM; //エラー番号をセット
      return NULL; //終了
    case I_SEMI: //中間コードが「;」の場合
      cip++; //中間コードポインタを次へ進める
      break; //打ち切る
    default: //以上のいずれにも該当しない場合
      err = ERR_SYNTAX; //エラー番号をセット
      break; //打ち切る
    } //中間コードで分岐の末尾

    if (err) //もしエラーが生じたら
      return NULL; //終了
  } //行末まで繰り返すの末尾
  return clp + *clp; //次に実行するべき行のポインタを持ち帰る
}

// RUN command handler
void irun() {

  if (*cip == I_STR) iload(); // ファイル名が続いていれば読み込んで実行

  unsigned char* lp; //行ポインタの一時的な記憶場所

  gstki = 0; //GOSUBスタックインデクスを0に初期化
  lstki = 0; //FORスタックインデクスを0に初期化
  clp = listbuf; //行ポインタをプログラム保存領域の先頭に設定

  while (*clp) { //行ポインタが末尾を指すまで繰り返す
    cip = clp + 3; //中間コードポインタを行番号の後ろに設定
    lp = iexe(); //中間コードを実行して次の行の位置を得る
    if (err) //もしエラーを生じたら
      return; //終了
    clp = lp; //行ポインタを次の行の位置へ移動
  } //行ポインタが末尾を指すまで繰り返すの末尾
}

// LIST command handler
void ilist() {

  if(*listbuf == 0) return; // 何も入力されていなければ表示しない

  short lineno; //表示開始行番号

  //表示開始行番号の設定
  if (*cip == I_NUM) //もしLIST命令に引数があったら
    lineno = getlineno(cip); //引数を読み取って表示開始行番号とする
  else //引数がなければ
    lineno = 0; //表示開始行番号を0とする

  //行ポインタを表示開始行番号へ進める
  for ( //次の手順で繰り返す
    clp = listbuf; //行ポインタを先頭行へ設定
    //末尾ではなくて表示開始行より前なら繰り返す
    *clp && (getlineno(clp) < lineno);
    clp += *clp); //行ポインタを次の行へ進める

  if(*cip == I_ALL) { // 引数にALLがあれば全行を表示
      cip++;
      while (*clp) { //行ポインタが末尾を指すまで繰り返す
          putnum(getlineno(clp), 0); //行番号を表示
          c_putch(' '); //空白を入れる
          putlist(clp + 3); //行番号より後ろを文字列に変換して表示
          if (err) //もしエラーが生じたら
              break; //繰り返しを打ち切る
          newline(); //改行
          clp += *clp; //行ポインタを次の行へ進める
      }
      return;
  }

  //リストを表示する
  if(*clp == 0) { // 末尾なら一行前を表示
      short prev_lineno;
      for ( //次の手順で繰り返す
              clp = listbuf; //行ポインタを先頭行へ設定
                             //末尾ではなくて表示開始行より前なら繰り返す
              *clp && (getlineno(clp) < lineno);
              clp += *clp) { //行ポインタを次の行へ進める
          prev_lineno = getlineno(clp); // linenoの一行前の行番号を取得
      }
      lineno = prev_lineno; // linenoを一行前に設定
      for ( //次の手順で繰り返す
              clp = listbuf; //行ポインタを先頭行へ設定
                             //末尾ではなくて表示開始行より前なら繰り返す
              *clp && (getlineno(clp) < lineno);
              clp += *clp); //行ポインタを次の行へ進める
  }
  lcd_cls(white, text);
  putnum(getlineno(clp), 0); //行番号を表示
  c_putch(' '); //空白を入れる
  putlist(clp + 3); //行番号より後ろを文字列に変換して表示
  if (err) //もしエラーが生じたら
      return; //繰り返しを打ち切る
  newline();

  //リストを表示する
  while (true) { //Escを押すと中断

      short chr = c_getch();
      if(chr == 0x1b) { // Escかキーボード入力の矢印キーか判断
          if(tud_cdc_available()){
              short next_chr = getchar();
              if(next_chr == 91){
                  if(tud_cdc_available()){
                      next_chr = getchar();
                      switch(next_chr){
                          case 65:
                            chr = CODE_UP;
                            break;
                          case 66:
                            chr = CODE_DOWN;
                            break;
                          case 67:
                            chr = CODE_RIGHT;
                            break;
                          case 68:
                            chr = CODE_LEFT;
                            break;
                      }
                  }
              }
          }
      }

      if(chr == CODE_UP){
          short prev_lineno;
          for ( //次の手順で繰り返す
            clp = listbuf; //行ポインタを先頭行へ設定
            //末尾ではなくて表示開始行より前なら繰り返す
            *clp && (getlineno(clp) < lineno);
            clp += *clp) { //行ポインタを次の行へ進める
              prev_lineno = getlineno(clp); // linenoの一行前の行番号を取得
          }
          if(lineno != prev_lineno){ // 一番初めの行なら処理しない
              lineno = prev_lineno; // linenoを一行前に設定
              for ( //次の手順で繰り返す
                      clp = listbuf; //行ポインタを先頭行へ設定
                                     //末尾ではなくて表示開始行より前なら繰り返す
                      *clp && (getlineno(clp) < lineno);
                      clp += *clp); //行ポインタを次の行へ進める

              lcd_cls(white, text);
              putnum(getlineno(clp), 0); //行番号を表示
              c_putch(' '); //空白を入れる
              putlist(clp + 3); //行番号より後ろを文字列に変換して表示
              if (err) //もしエラーが生じたら
                  return; //繰り返しを打ち切る
              newline();
          }

          sleep_ms(30); // チャタリング対策
          while(ioexp_getkey(0) == CODE_UP);
          sleep_ms(30); // チャタリング対策

      }else if((chr == CODE_DOWN) && *(clp + *clp)){ // clp+*clpが末尾なら処理しない
          clp += *clp; //行ポインタを次の行へ進める
          lineno = getlineno(clp);

          lcd_cls(white, text);
          putnum(getlineno(clp), 0); //行番号を表示
          c_putch(' '); //空白を入れる
          putlist(clp + 3); //行番号より後ろを文字列に変換して表示
          if (err) //もしエラーが生じたら
              return; //繰り返しを打ち切る
          newline();

          sleep_ms(30); // チャタリング対策
          while(ioexp_getkey(0) == CODE_DOWN);
          sleep_ms(30); // チャタリング対策
      }else if(chr == 0x1b){ // EscでLISTモードを抜ける
          lcd_cls(white, text);
          return;
      }
  }
  //newline(); //改行
  //clp += *clp; //行ポインタを次の行へ進める
}

//NEW command handler
void inew(void) {
  unsigned short i; //ループカウンタ

  //変数と配列の初期化
  for (i = 0; i < 26; i++) //変数の数だけ繰り返す
    var[i] = 0; //変数を0に初期化
  for (i = 0; i < SIZE_ARRY; i++) //配列の数だけ繰り返す
    arr[i] = 0; //配列を0に初期化

  //実行制御用の初期化
  gstki = 0; //GOSUBスタックインデクスを0に初期化
  lstki = 0; //FORスタックインデクスを0に初期化
  *listbuf = 0; //プログラム保存領域の先頭に末尾の印を置く
  clp = listbuf; //行ポインタをプログラム保存領域の先頭に設定
  lpc_clear(); //行ポインタのキャッシュを捨てる
}

// 16進数のファイル出力
void fputHexnum(short value, uint8_t d, FIL *fp) {

  uint16_t hex = (uint16_t)value;
  uint16_t h;
  uint16_t dig;

  if (hex >= 0x1000) dig = 4;
  else if (hex >= 0x100) dig = 3;
  else if (hex >= 0x10) dig = 2;
  else dig = 1;

  if (d != 0 && d > dig) dig = d;

  for (uint8_t i = 0; i < 4; i++) {
    h = ( hex >> (12 - i * 4) ) & 0x0f;
    lbuf[i] = h <= 9 ? h + '0': h + 'A' - 10;
  }
  lbuf[4] = 0;
  f_printf(fp, &lbuf[4-dig]);
}

// 2進数のファイル出力
void fputBinnum(int16_t value, uint8_t d, FIL *fp) {

  uint16_t bin = (uint16_t)value;
  uint16_t  dig = 0;

  for (uint8_t i=0; i < 16; i++) {
    if ( (0x8000>>i) & bin ) {
      dig = 15 - i;
      break;
    }
  }
  dig++;
  
  if (d > dig) 
    dig = d;

  for (int8_t i=dig-1; i>=0; i--)
    f_putc((bin & (1<<i)) ? '1':'0', fp);

}

#ifdef _PROG_
//Listing 1 line of i-code to file
void fputlist(FIL *fp, unsigned char* ip) {
    unsigned char i;

    while (*ip != I_EOL) {
        // Case keyword
        if (*ip < SIZE_KWTBL) {
            f_puts(kwtbl[*ip], fp);
            if (!nospacea(*ip)) f_putc(' ', fp);
            if (*ip == I_REM) {
                ip++;
                i = *ip++;
                while (i--) {
                    f_putc(*ip++, fp);
                }
                return;
            }
            ip++;
        }
        else

            // Case numeric
            if (*ip == I_NUM) {
                ip++;
                f_printf(fp, "%d", *ip | *(ip + 1) << 8);
                ip += 2;
                if (!nospaceb(*ip)) f_putc(' ', fp);
            }
            else

    //16進定数の処理
    if (*ip == I_HEXNUM) { //もし16進定数なら
      ip++; //ポインタを値へ進める
      f_putc('$', fp); //空白を表示
      fputHexnum(*ip | *(ip + 1) << 8, 2, fp); //値を取得して表示
      ip += 2; //ポインタを次の中間コードへ進める
      if (!nospaceb(*ip)) //もし例外にあたらなければ
        f_putc(' ', fp); //空白を表示
    }
    else

    //2進定数の処理
    if (*ip == I_BINNUM) { //もし2進定数なら
      ip++; //ポインタを値へ進める
      f_putc('`', fp); //"`"を表示
      if (*(ip + 1))
          fputBinnum(*ip | *(ip + 1) << 8, 16, fp); //値を取得して16桁で表示
      else
          fputBinnum(*ip, 8, fp);  //値を取得して8桁で表示
      ip += 2; //ポインタを次の中間コードへ進める
      if (!nospaceb(*ip)) //もし例外にあたらなければ
        f_putc(' ', fp); //空白を表示
    }
    else 

                // Case variable
                if (*ip == I_VAR) {
                    ip++;
                    f_putc(*ip++ + 'A', fp);
                    if (!nospaceb(*ip)) f_putc(' ', fp);
                }
                else

                    // Case string
                    if (*ip == I_STR) {
                        char c;

                        c = '\"';
                        ip++;
                        for (i = *ip; i; i--) {
                            if (*(ip + i) == '\"') {
                                c = '\'';
                                break;
                            }
                        }

                        f_putc(c, fp);
                        i = *ip++;
                        while (i--) f_putc(*ip++, fp);
                        f_putc(c, fp);
                        if (*ip == I_VAR) f_putc(' ', fp);
                    }

        // Nothing match, I think, such case is impossible
                    else {
                        err = ERR_SYS;
                        return;
                    }
    }
}

//SAVE command handler
void isave() {
    FIL fp;
    char buf[256];
    unsigned char len;
    unsigned char i;

    sd_card_t *pSD = sd_get_by_num(0);
    FRESULT fr = f_mount(&pSD->fatfs, pSD->pcName, 1);
    if (FR_OK != fr) {
        err = ERR_SDMOUNT;
        return;
    }
    fr = f_chdrive(pSD->pcName);
    if (FR_OK != fr) {
        err = ERR_SDCHDRV;
        return;
    }

    if (*cip != I_STR) {
        err = ERR_SYNTAX;
        return;
    }
    cip++;

    len = *cip;
    if (len == 0) {
        err = ERR_SYNTAX;
        return;
    }
    cip++;

    for (i = 0; i < len; i++) buf[i] = *cip++;
    buf[i] = 0;

    if (*cip != I_EOL) {
        err = ERR_SYNTAX;
        return;
    }

// ファイルが既に存在している場合の処理
//    f_open(&fp, buf, FA_CREATE_NEW | FA_READ); // Windows style
//                            //fp = fopen(buf, "r"); // Linux style
//    if (&fp != NULL) {
//        f_close(&fp);
//        err = ERR_FEXIST;
//        return;
//    }

    fr = f_open(&fp, buf, FA_CREATE_ALWAYS | FA_WRITE);
    if (FR_OK != fr && FR_EXIST != fr) {
        err = ERR_FNOPEN;
        return;
    }

    clp = listbuf;
    while (*clp) {
        f_printf(&fp, "%d ", getlineno(clp));
        fputlist(&fp, clp + 3);
        if (err) break;
        f_printf(&fp, "\n");
        clp += *clp;
    }
    f_close(&fp);
    fr = f_unmount(pSD->pcName);
    if (FR_OK == fr) {
        pSD->mounted = false;
    } else {
        printf("f_unmount error: %s (%d)\n", FRESULT_str(fr), fr);
    }
    pSD->m_Status |= STA_NOINIT; // in case medium is removed
    sd_card_detect(pSD);
}

//LOAD command handler
void iload() {
    FIL fp;
    char buf[256];
    unsigned char len;
    unsigned char i;

    sd_card_t *pSD = sd_get_by_num(0);
    FRESULT fr = f_mount(&pSD->fatfs, pSD->pcName, 1);
    if (FR_OK != fr) {
        err = ERR_SDMOUNT;
        return;
    }
    fr = f_chdrive(pSD->pcName);
    if (FR_OK != fr) {
        err = ERR_SDCHDRV;
        return;
    }

    if (*cip != I_STR) {
        err = ERR_SYNTAX;
        return;
    }
    cip++;

    len = *cip;
    if (len == 0) {
        err = ERR_SYNTAX;
        return;
    }
    cip++;

    for (i = 0; i < len; i++) buf[i] = *cip++;
    buf[i] = 0;

    if (*cip != I_EOL) {
        err = ERR_SYNTAX;
        return;
    }

    fr = f_open(&fp, buf, FA_OPEN_EXISTING | FA_READ);
    if (FR_OK != fr && FR_EXIST != fr) {
        err = ERR_FNFOUND;
        return;
    }

    inew();

    while (f_gets(buf, SIZE_LINE, &fp)) {
        for (i = 0; c_isprint(buf[i]); i++) lbuf[i] = buf[i];
        lbuf[i] = 0;
        len = toktoi();
        if (err) break;
        if (*ibuf != I_NUM) {
            err = ERR_SYNTAX;
            break;
        }
        *ibuf = len;
        inslist();
        if (err) break;
    }
    f_close(&fp);
    fr = f_unmount(pSD->pcName);
    if (FR_OK == fr) {
        pSD->mounted = false;
    } else {
        printf("f_unmount error: %s (%d)\n", FRESULT_str(fr), fr);
    }
    pSD->m_Status |= STA_NOINIT; // in case medium is removed
    sd_card_detect(pSD);
}

bool iload_autorun() {

    FIL fp;
    char buf[256];
    unsigned char len;
    unsigned char i;

    sd_card_t *pSD = sd_get_by_num(0);
    FRESULT fr = f_mount(&pSD->fatfs, pSD->pcName, 1);
    if (FR_OK != fr) {
        return 1;
    }
    fr = f_chdrive(pSD->pcName);
    if (FR_OK != fr) {
        return 1;
    }

    sprintf(buf, "AUTORUN.TXT");

    fr = f_open(&fp, buf, FA_OPEN_EXISTING | FA_READ);
    if (FR_OK != fr && FR_EXIST != fr) {
        return 1;
    }

    inew();

    while (f_gets(buf, SIZE_LINE, &fp)) {
        for (i = 0; c_isprint(buf[i]); i++) lbuf[i] = buf[i];
        lbuf[i] = 0;
        len = toktoi();
        if (err) break;
        if (*ibuf != I_NUM) {
            err = ERR_SYNTAX;
            break;
        }
        *ibuf = len;
        inslist();
        if (err) break;
    }
    f_close(&fp);
    fr = f_unmount(pSD->pcName);
    if (FR_OK == fr) {
        pSD->mounted = false;
    } else {
        printf("f_unmount error: %s (%d)\n", FRESULT_str(fr), fr);
    }
    pSD->m_Status |= STA_NOINIT; // in case medium is removed
    sd_card_detect(pSD);

    return 0;

}
#endif

//DELETE command handler
void idelete() {
    FIL fp;
    char buf[256];
    unsigned char len;
    unsigned char i;

    sd_card_t *pSD = sd_get_by_num(0);
    FRESULT fr = f_mount(&pSD->fatfs, pSD->pcName, 1);
    if (FR_OK != fr) {
        err = ERR_SDMOUNT;
        return;
    }
    fr = f_chdrive(pSD->pcName);
    if (FR_OK != fr) {
        err = ERR_SDCHDRV;
        return;
    }

    if (*cip != I_STR) {
        err = ERR_SYNTAX;
        return;
    }
    cip++;

    len = *cip;
    if (len == 0) {
        err = ERR_SYNTAX;
        return;
    }
    cip++;

    for (i = 0; i < len; i++) buf[i] = *cip++;
    buf[i] = 0;

    if (*cip != I_EOL) {
        err = ERR_SYNTAX;
        return;
    }

    fr = f_unlink(buf);
    if (FR_OK != fr && FR_EXIST != fr) {
        err = ERR_FNOPEN;
        return;
    }

    fr = f_unmount(pSD->pcName);
    if (FR_OK == fr) {
        pSD->mounted = false;
    } else {
        printf("f_unmount error: %s (%d)\n", FRESULT_str(fr), fr);
    }
    pSD->m_Status |= STA_NOINIT; // in case medium is removed
    sd_card_detect(pSD);
}

//Command precessor
void icom() {
  cip = ibuf; //中間コードポインタを中間コードバッファの先頭に設定

  switch (*cip) { //中間コードポインタが指し示す中間コードによって分岐

  case I_NEW: //I_NEWの場合（NEW命令）
    cip++; //中間コードポインタを次へ進める
    if (*cip == I_EOL) //もし行末だったら
      inew(); //NEW命令を実行
    else //行末でなければ
      err = ERR_SYNTAX; //エラー番号をセット
    break; //打ち切る

  case I_LIST: //I_LISTの場合（LIST命令）
    cip++; //中間コードポインタを次へ進める
    if (*cip == I_EOL || //もし行末か、あるいは
      *(cip + 3) == I_EOL || //続いて引数があれば
      *cip == I_ALL)
      ilist(); //LIST命令を実行
    else //そうでなければ
      err = ERR_SYNTAX; //エラー番号をセット
    break; //打ち切る

  case I_RUN: //I_RUNの場合（RUN命令）
    cip++; //中間コードポインタを次へ進める
    irun(); //RUN命令を実行
    break; //打ち切る

#ifdef _PROG_
  case I_SAVE:
    cip++;
    isave();
    break;
  case I_LOAD:
    cip++;
    iload();
    break;
  case I_DELETE:
    cip++;
    idelete();
    break;
#endif

  default: //どれにも該当しない場合
    iexe(); //中間コードを実行
    break; //打ち切る
  }
}

// Print OK or error message
void error() {
  if (err) { //もし「OK」ではなかったら

    //もしプログラムの実行中なら（cipがリストの中にあり、clpが末尾ではない場合）
    if (cip >= listbuf && cip < listbuf + SIZE_LIST && *clp)
    {
      newline(); //改行
      c_puts("LINE:"); //「LINE:」を表示
      putnum(getlineno(clp), 0); //行番号を調べて表示
      c_putch(' '); //空白を表示
      putlist(clp + 3); //リストの該当行を表示
    }
    else //指示の実行中なら
    {
      newline(); //改行
      c_puts("YOU TYPE: "); //「YOU TYPE:」を表示
      c_puts(lbuf); //文字列バッファの内容を表示
    }
  } //もし「OK」ではなかったらの末尾

  newline(); //改行
  c_puts(errmsg[err]); //「OK」またはエラーメッセージを表示
  newline(); //改行
  err = 0; //エラー番号をクリア
}

// AUTORUN.TXTが存在していれば実行する
void autorun() {

  if(!iload_autorun()) irun();

}

/*
  TOYOSHIKI Tiny BASIC
  The BASIC entry point
*/

void basic() {
  unsigned char len; //中間コードの長さ

  inew(); //実行環境を初期化

  //起動メッセージ
  c_puts("TOYOSHIKI TINY BASIC"); //「TOYOSHIKI TINY BASIC」を表示
  newline(); //改行
  c_puts(STR_EDITION); //版を区別する文字列を表示
  c_puts(" EDITION"); //「 EDITION」を表示
  newline(); //改行
  c_puts("version ");
  c_puts(STR_VERSION);
  newline(); //改行
  error(); //「OK」またはエラーメッセージを表示してエラー番号をクリア

  // SWが押されていなければAUTORUN.TXTを実行する
  if(gpio_get(PIN_SW)) autorun();
  if (err) error();

  //端末から1行を入力して実行
  while (1) { //無限ループ
    c_putch('>'); //プロンプトを表示
    c_gets(); //1行を入力

    //1行の文字列を中間コードの並びに変換
    len = toktoi(); //文字列を中間コードに変換して長さを取得
    if (err) { //もしエラーが発生したら
      error(); //エラーメッセージを表示してエラー番号をクリア
      continue; //繰り返しの先頭へ戻ってやり直し
    }

    //中間コードの並びがプログラムと判断される場合
    if (*ibuf == I_NUM) { //もし中間コードバッファの先頭が行番号なら
      *ibuf = len; //中間コードバッファの先頭を長さに書き換える
      inslist(); //中間コードの1行をリストへ挿入
      if (err) //もしエラーが発生したら
        error(); //エラーメッセージを表示してエラー番号をクリア
      continue; //繰り返しの先頭へ戻ってやり直し
    }

    //中間コードの並びが命令と判断される場合
    icom(); //実行する
    error(); //エラーメッセージを表示してエラー番号をクリア

  } //無限ループの末尾
}
