TTtensan/NERD-HPC/software/src/ir.c

#include <inttypes.h>
#include "stdio.h"
#include "pico/stdlib.h"
#include "pin.h"
#include "hardware/pwm.h"
#include "ir.h"

#define IR_INTERVAL_MAX 1280

uint64_t arry_ir_interval[IR_INTERVAL_MAX] = {0};

void ir_put(bool value) {
  if(value) {
    pwm_set_chan_level(ir_slice_num, pwm_gpio_to_channel(PIN_IR_TX), ir_wrap / 2); // デューティ50%
  } else {
    pwm_set_chan_level(ir_slice_num, pwm_gpio_to_channel(PIN_IR_TX), ir_wrap); // デューティ50%
  }
}

bool ir_get() {
  return !gpio_get(PIN_IR_RX);
}

void ir_copy() {
    for(int i=0; i<IR_INTERVAL_MAX; i++) arry_ir_interval[i] = 0;
    //to_us_since_boot(get_absolute_time());
    //printf( "%" PRIu64 "\n", to_us_since_boot(get_absolute_time()));
    int index = 0;
    while(true) {
        // 1回のループでON区間とOFF区間の2要素を書くので、
        // 2要素分の空きが無くなった時点で打ち切る。
        // 以前はメッセージを出すだけで書き込みを続けており、
        // 長い信号を受けると配列の外を壊していた
        if(index > IR_INTERVAL_MAX - 2) {
            printf("index over flow\n");
            return;
        }
        if(!gpio_get(PIN_IR_RX)) {
            uint64_t count_start = to_us_since_boot(get_absolute_time());
            while(!gpio_get(PIN_IR_RX));
            arry_ir_interval[index] = to_us_since_boot(get_absolute_time()) - count_start;
            index++;
            count_start = to_us_since_boot(get_absolute_time());
            while(gpio_get(PIN_IR_RX)) {
                if(!gpio_get(PIN_SW))
                {
                    printf("copied\n");
                    sleep_ms(1000);
                    return;
                }
            }
            arry_ir_interval[index] = to_us_since_boot(get_absolute_time()) - count_start;
            index++;
        }

    }
}

void ir_send_copied() {
    while(gpio_get(PIN_SW));
    printf("send\n");
    sleep_ms(500);
    bool on_off = true;
    for(int i=0; i<IR_INTERVAL_MAX; i++) {
        pwm_set_enabled(pwm_gpio_to_slice_num(PIN_IR_TX), on_off);
        on_off = !on_off;
        if(arry_ir_interval[i] == 0) return;
        sleep_us(arry_ir_interval[i]);
    }
}
