TTtensan/NERD-HPC/software/src/io.h

#ifndef IO_H_
#define IO_H_

#ifdef __cplusplus
extern "C" {
#endif

static char event_str[128];

void io_button_callback(uint gpio, uint32_t events);
void io_init();
void io_set_dir(uint gpio, bool out);
void io_pull_up(uint gpio);
void io_pull_down(uint gpio);
void io_disable_pulls(uint gpio);
void io_put(uint gpio, bool value);
bool io_get(uint gpio);
void io_uart_send(uint8_t data);
uint8_t io_uart_receive();
void io_i2c_master_init();
void io_i2c_slave_init();
void io_i2c_set_address(uint8_t addr);
void io_i2c_send(uint8_t data);
uint8_t io_i2c_receive();
void gpio_event_string(char *buf, uint32_t events);

#ifdef __cplusplus
}
#endif

#endif
